samunemeth/E-paper-Clock/src/display_helper/custom_icons.h

#ifndef CUSTOM_ICONS_H
#define CUSTOM_ICONS_H

#include <pgmspace.h>

#define refresh_xbm_width 12
#define refresh_xbm_height 12
static unsigned char refresh_xbm_bits[] PROGMEM = {
    0x00, 0xf0, 0xf0, 0xf4, 0xfc, 0xf7, 0x0c, 0xf7, 0x86, 0xf7, 0x02, 0xf0,
    0x00, 0xf4, 0x1e, 0xf6, 0x0e, 0xf3, 0xfe, 0xf3, 0xf2, 0xf0, 0x00, 0xf0};

#define battery_xbm_width 16
#define battery_xbm_height 10
static unsigned char battery_multiple_xbm_bits[5][20] PROGMEM = {
    {0xff, 0x3f, 0xff, 0x3f, 0x03, 0xf0, 0x03, 0xf0, 0x03, 0xf0, 0x03, 0xf0,
     0x03, 0xf0, 0x03, 0xf0, 0xff, 0x3f, 0xff, 0x3f},
    {0xff, 0x3f, 0xff, 0x3f, 0x03, 0xf0, 0x1b, 0xf0, 0x1b, 0xf0, 0x1b, 0xf0,
     0x1b, 0xf0, 0x03, 0xf0, 0xff, 0x3f, 0xff, 0x3f},
    {0xff, 0x3f, 0xff, 0x3f, 0x03, 0xf0, 0xdb, 0xf0, 0xdb, 0xf0, 0xdb, 0xf0,
     0xdb, 0xf0, 0x03, 0xf0, 0xff, 0x3f, 0xff, 0x3f},
    {0xff, 0x3f, 0xff, 0x3f, 0x03, 0xf0, 0xdb, 0xf6, 0xdb, 0xf6, 0xdb, 0xf6,
     0xdb, 0xf6, 0x03, 0xf0, 0xff, 0x3f, 0xff, 0x3f},
    {0xff, 0x3f, 0xff, 0x3f, 0x03, 0xf0, 0x63, 0xf4, 0xf3, 0xf6, 0xdb, 0xf3,
     0x8b, 0xf1, 0x03, 0xf0, 0xff, 0x3f, 0xff, 0x3f},
};

#endif
